Sillybutts/SillyMaxx1400/STLs/Barrels/5x Elite.stl

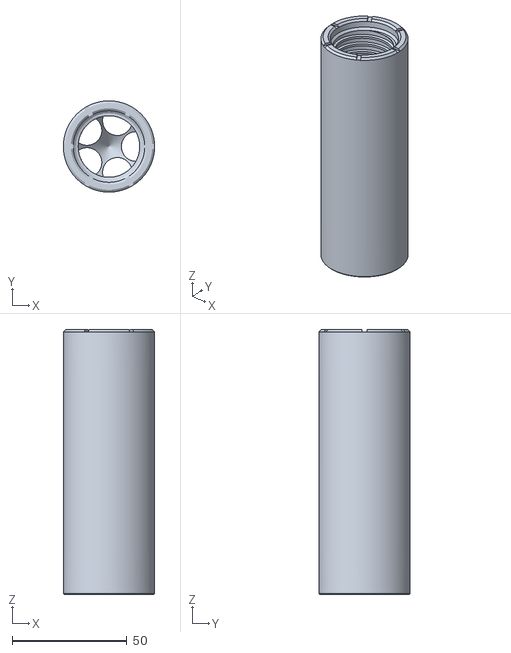
[picture p50: CAD file, 2022-04-14]
STLs/Barrels/5x Elite.stl
39.8 x 39.8 x 115.5
