Sillybutts/SillyMaxx1400/STLs/Gray/Trigger Guard.stl

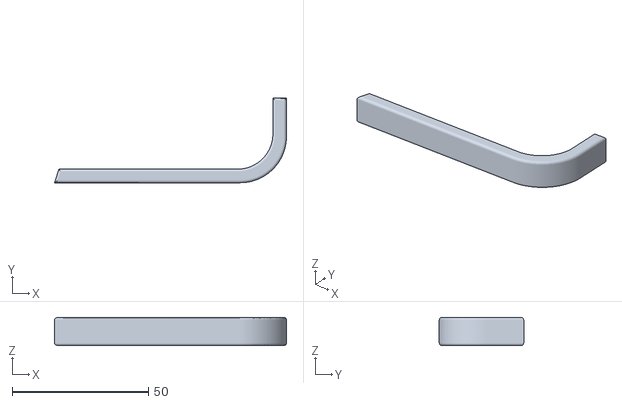
[picture p51: CAD file, 2022-04-14]
STLs/Gray/Trigger Guard.stl
85.2 x 31.0 x 10.4
