Sillybutts/SillyMaxx1400/STLs/Orange/Attachments for top of Faux Tank/TopSight.stl

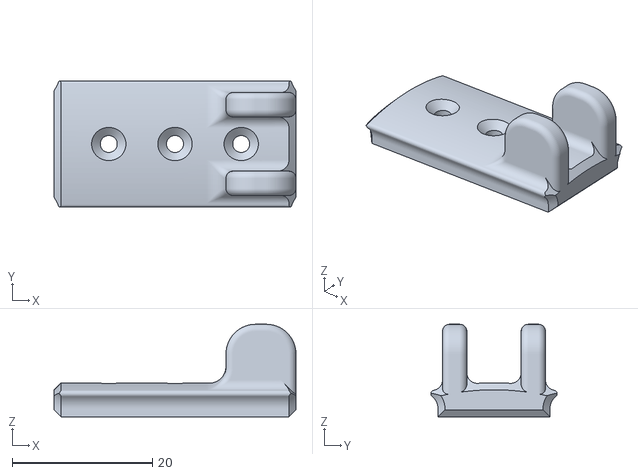
[picture p52: CAD file, 2022-04-14]
STLs/Orange/Attachments for top of Faux Tank/TopSight.stl
34.5 x 18.0 x 13.2
