Sillybutts/SillyMaxx1400/STLs/Orange/TriggerB.stl

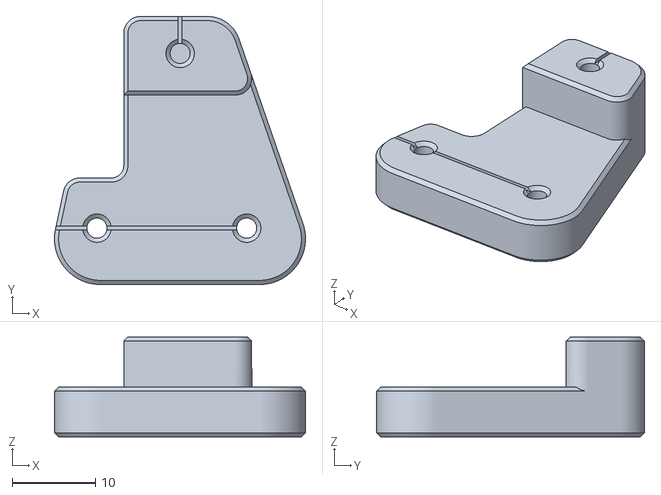
[picture p53: CAD file, 2022-04-14]
STLs/Orange/TriggerB.stl
30.2 x 32.2 x 12.0
