Sillybutts/SillyMaxx1400/STLs/Red/BackTube4PRINTTWO.stl

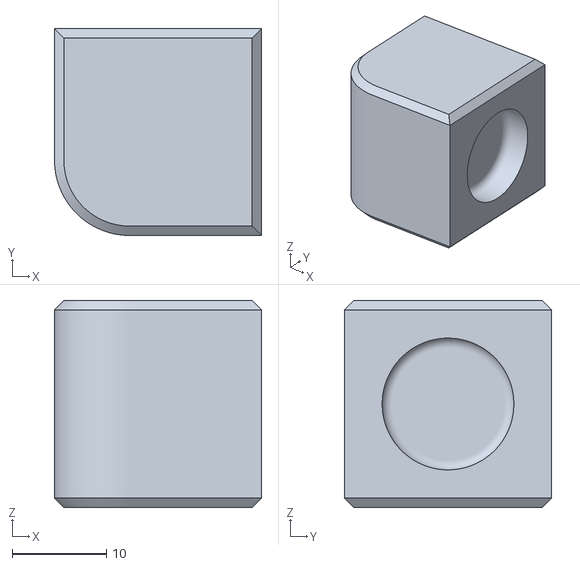
[picture p54: CAD file, 2022-04-14]
STLs/Red/BackTube4PRINTTWO.stl
22.0 x 22.0 x 22.0
