Sillybutts/SillyMaxx1400/STLs/Yellow/PumpGrip.stl

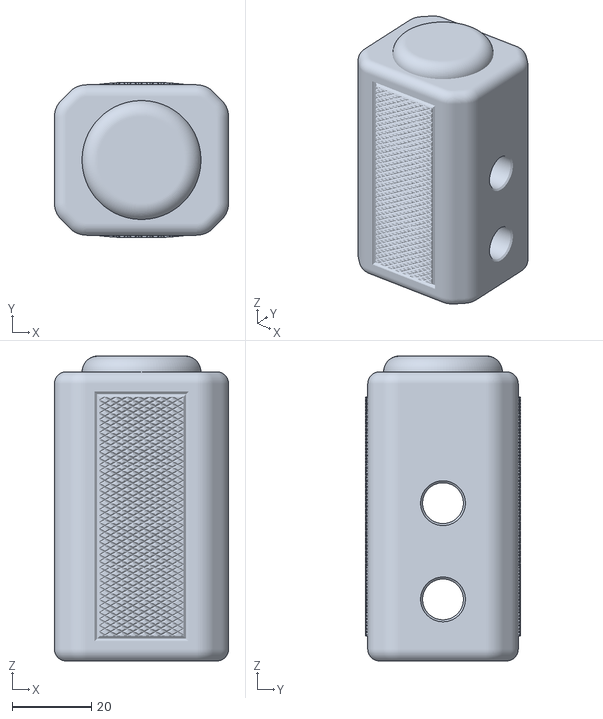
[picture p55: CAD file, 2022-04-14]
STLs/Yellow/PumpGrip.stl
44.0 x 39.1 x 77.0
