Sillybutts/SillyMaxx1400/STLs/Barrels/Mega.stl

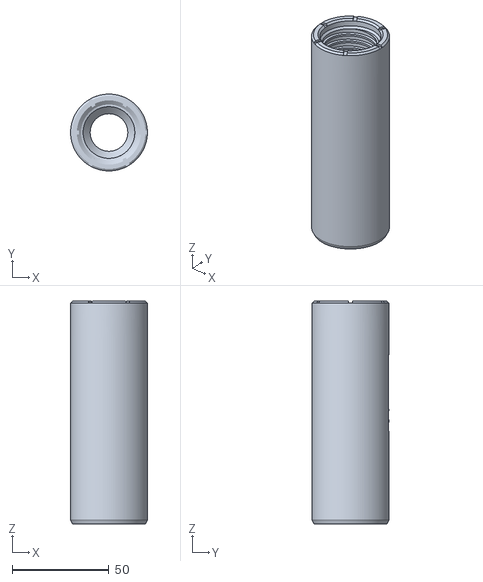
[picture p56: CAD file, 2022-04-14]
STLs/Barrels/Mega.stl
39.8 x 39.8 x 115.5
