Sillybutts/SillyMaxx1400/STLs/Gray/Back Cover.stl

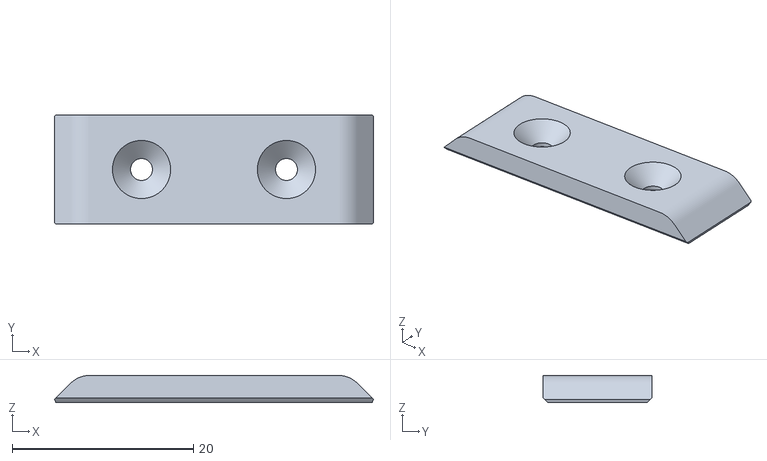
[picture p57: CAD file, 2022-04-14]
STLs/Gray/Back Cover.stl
35.2 x 12.0 x 3.00
