Sillybutts/SillyMaxx1400/STLs/Orange/Attachments for top of Faux Tank/MXL Ammo Holder.stl

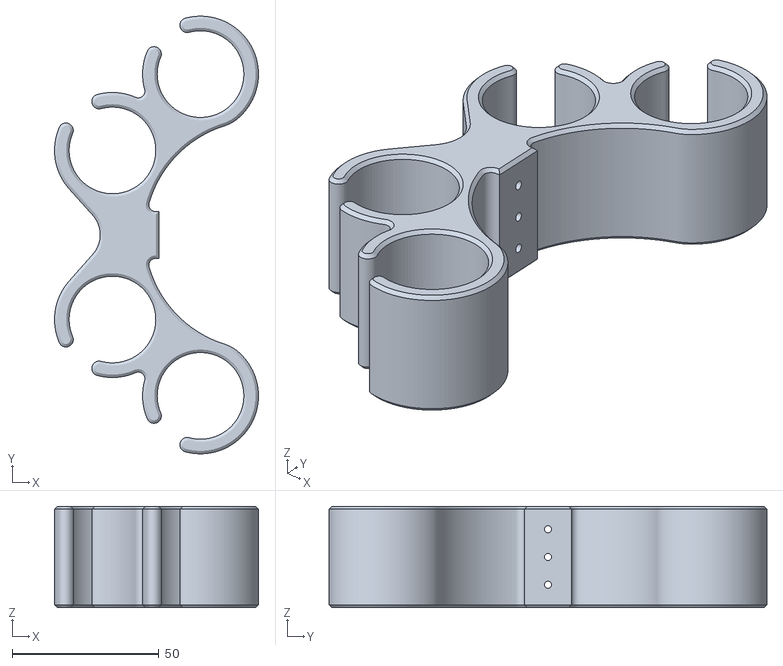
[picture p58: CAD file, 2022-04-14]
STLs/Orange/Attachments for top of Faux Tank/MXL Ammo Holder.stl
69.5 x 149.1 x 34.5
