Sillybutts/SillyMaxx1400/STLs/Orange/TriggerC.stl

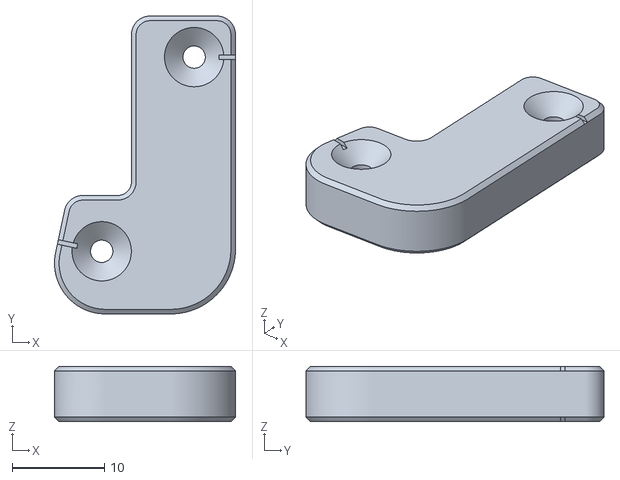
[picture p59: CAD file, 2022-04-14]
STLs/Orange/TriggerC.stl
19.6 x 32.2 x 6.00
