Sillybutts/SillyMaxx1400/STLs/Red/Faux Tank wAttachmentSlot A.stl

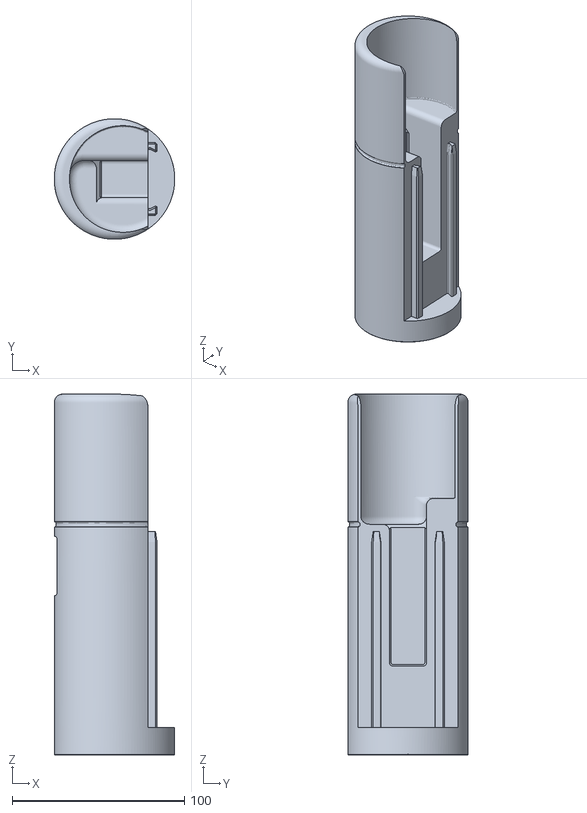
[picture p60: CAD file, 2022-04-14]
STLs/Red/Faux Tank wAttachmentSlot A.stl
70.0 x 70.0 x 209.8
