Sillybutts/SillyMaxx1400/STLs/Barrels/halfinchPVC SMOOTH.stl

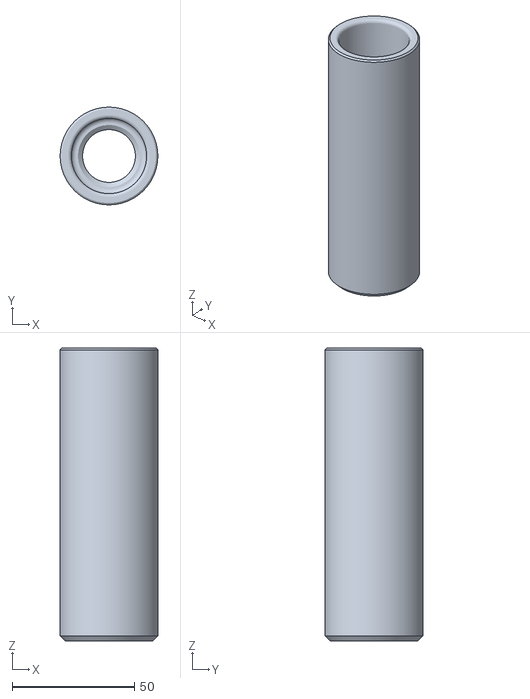
[picture p61: CAD file, 2022-04-14]
STLs/Barrels/halfinchPVC SMOOTH.stl
40.0 x 40.0 x 120.0
