Sillybutts/SillyMaxx1400/STLs/Gray/SmallCover.stl

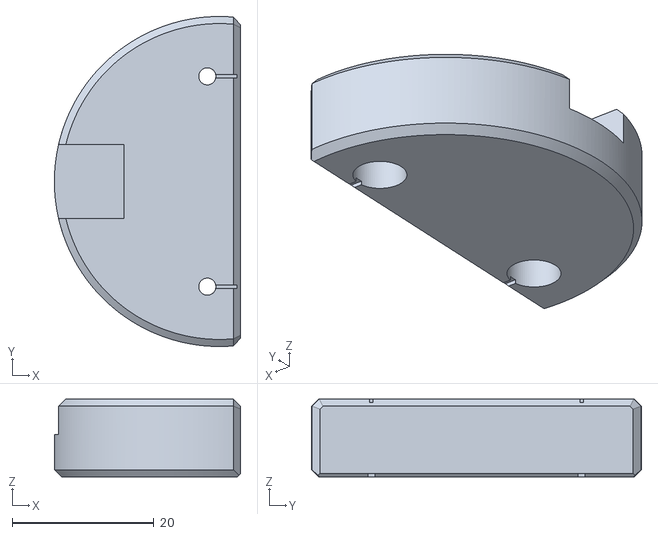
[picture p62: CAD file, 2022-04-14]
STLs/Gray/SmallCover.stl
26.3 x 46.6 x 11.0
