Sillybutts/SillyMaxx1400/STLs/Orange/Top Front Cap.stl

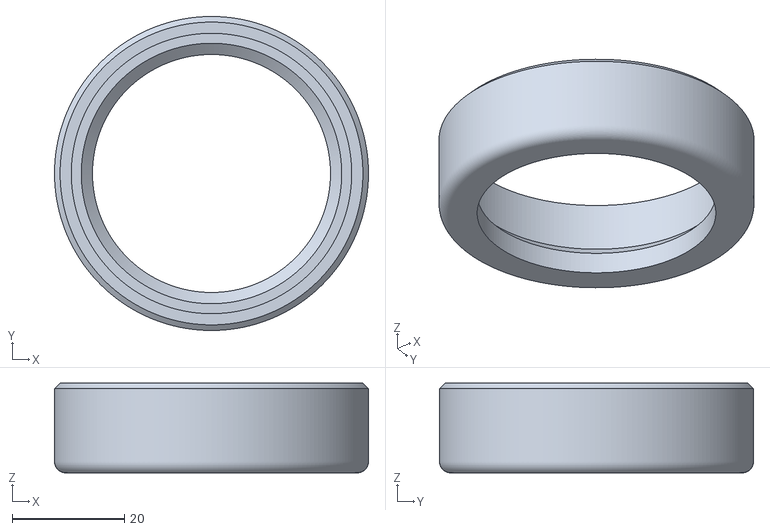
[picture p63: CAD file, 2022-04-14]
STLs/Orange/Top Front Cap.stl
56.0 x 56.0 x 16.0
