Sillybutts/SillyMaxx1400/STLs/Red/BackTube1.stl

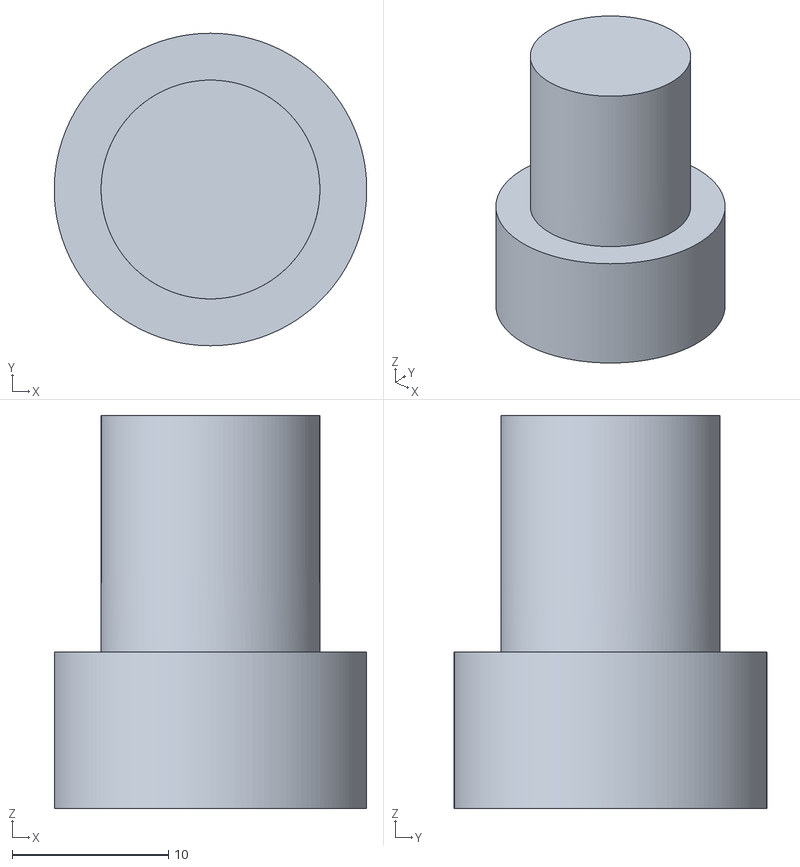
[picture p64: CAD file, 2022-04-14]
STLs/Red/BackTube1.stl
20.0 x 20.0 x 25.1
