Sillybutts/SillyMaxx1400/STLs/Barrels/3x Elite.stl

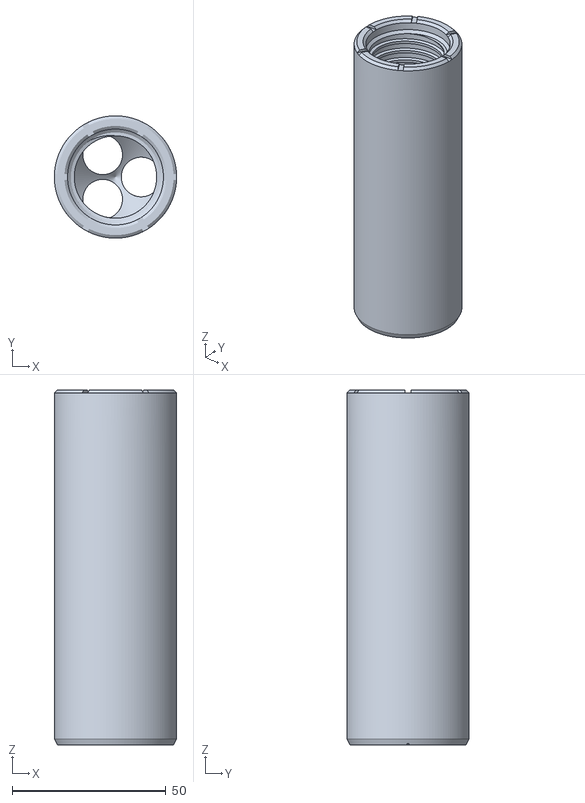
[picture p65: CAD file, 2022-04-14]
STLs/Barrels/3x Elite.stl
39.8 x 39.8 x 115.5
