Sillybutts/SillyMaxx1400/STLs/Gray/GripFrameB.stl

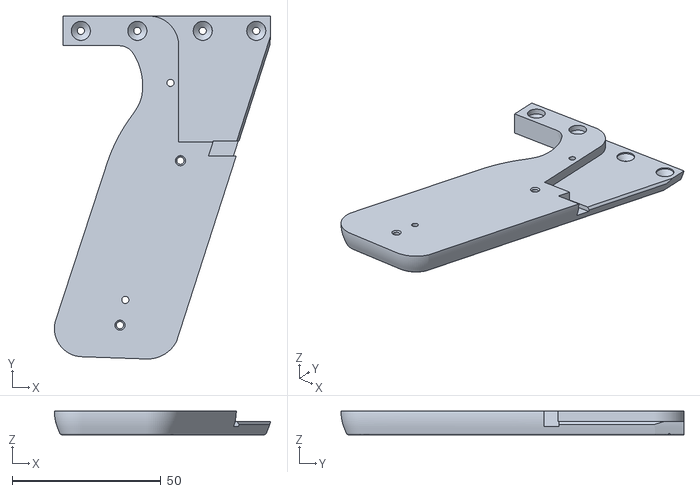
[picture p66: CAD file, 2022-04-14]
STLs/Gray/GripFrameB.stl
72.7 x 115.4 x 8.00
