Sillybutts/SillyMaxx1400/STLs/Red/Faux Tank B.stl

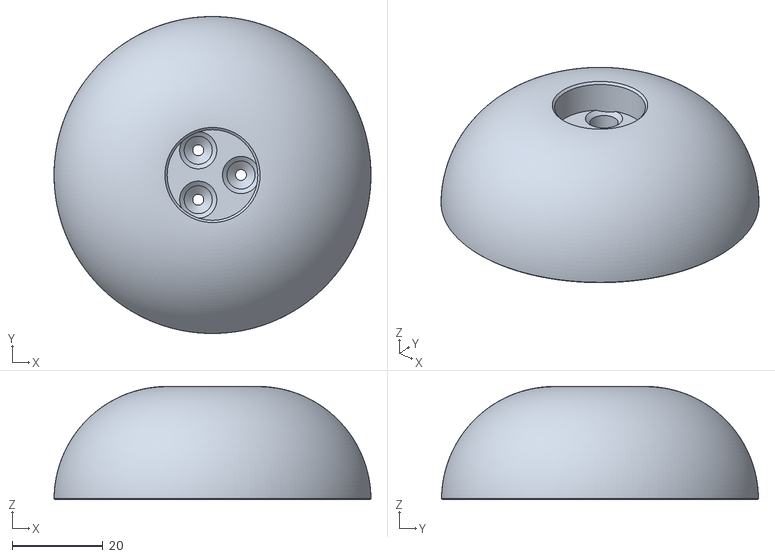
[picture p67: CAD file, 2022-04-14]
STLs/Red/Faux Tank B.stl
70.0 x 70.0 x 25.0
