Sillybutts/SillyMaxx1400/STLs/Barrels/MXL Trivictus.stl

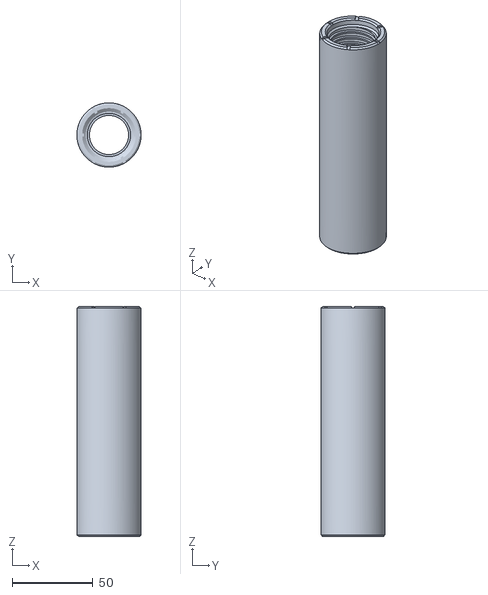
[picture p68: CAD file, 2022-04-14]
STLs/Barrels/MXL Trivictus.stl
39.8 x 39.8 x 142.5
