Sillybutts/SillyMaxx1400/STLs/Gray/Sling Point.stl

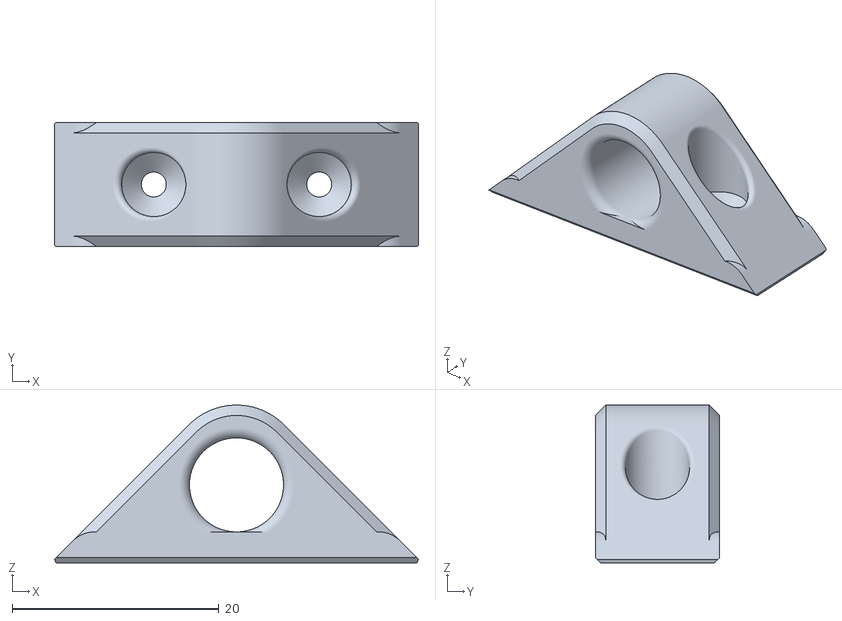
[picture p69: CAD file, 2022-04-14]
STLs/Gray/Sling Point.stl
35.2 x 12.0 x 15.3
