Sillybutts/SillyMaxx1400/STLs/Red/BackTube2PRINTTWO.stl

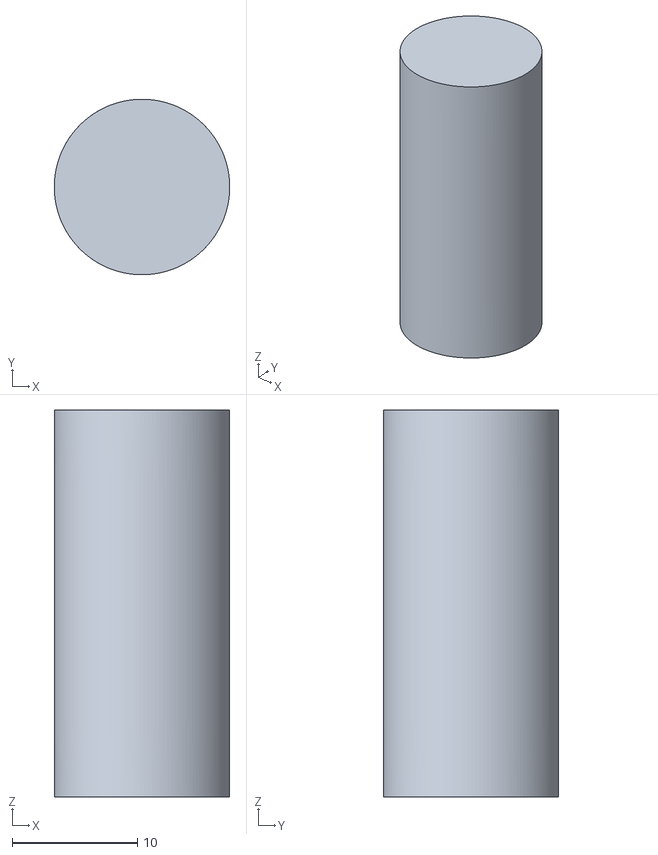
[picture p70: CAD file, 2022-04-14]
STLs/Red/BackTube2PRINTTWO.stl
14.0 x 14.0 x 30.9
