Sillybutts/SillyMaxx1400/STLs/Gray/FrontBlock wSight.stl

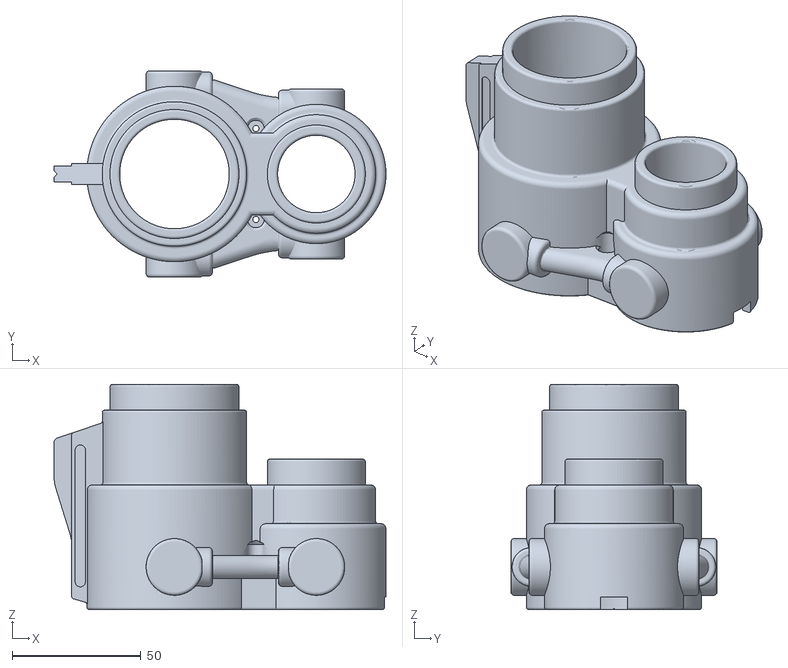
[picture p71: CAD file, 2022-04-14]
STLs/Gray/FrontBlock wSight.stl
128.7 x 80.0 x 87.4
