Sillybutts/SillyMaxx1400/STLs/Gray/BodyBlockA.stl

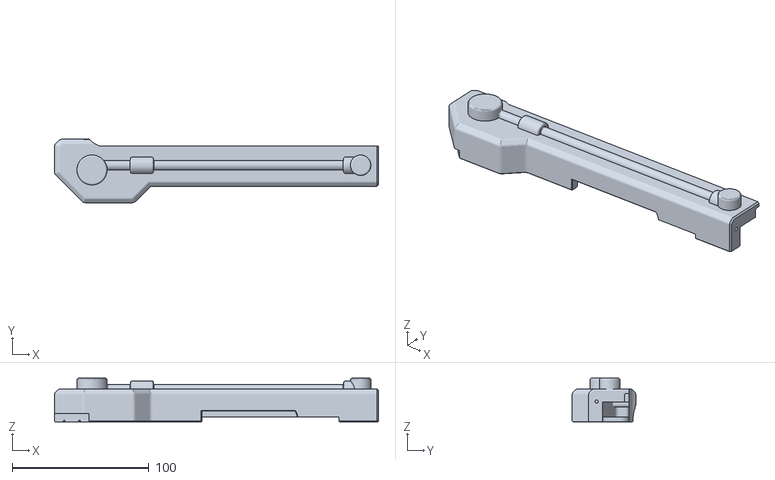
[picture p72: CAD file, 2022-04-14]
STLs/Gray/BodyBlockA.stl
237.0 x 46.5 x 32.0
