Sillybutts/SillyMaxx1400/STLs/Gray/BodyBlockC.stl

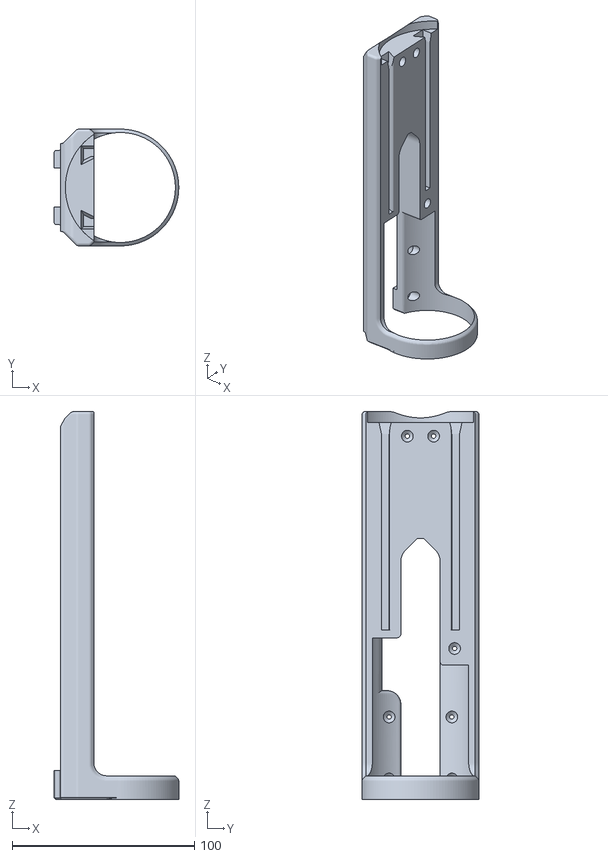
[picture p73: CAD file, 2022-04-14]
STLs/Gray/BodyBlockC.stl
68.3 x 64.1 x 212.8
