Sillybutts/SillyMaxx1400/STLs/Gray/FrontBlock NoSight.stl

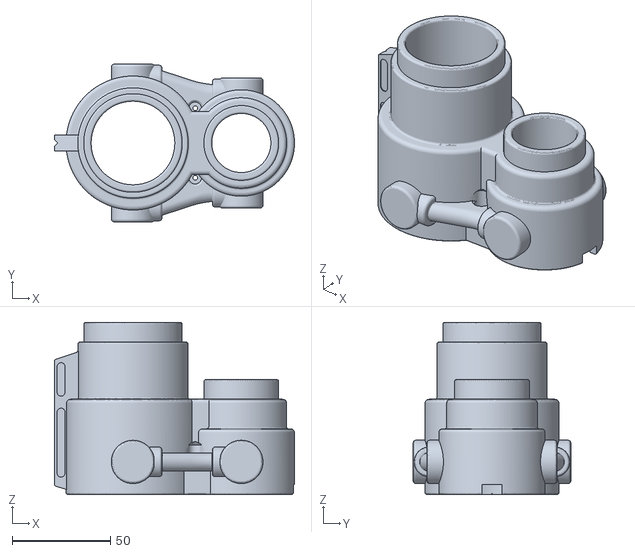
[picture p74: CAD file, 2022-04-14]
STLs/Gray/FrontBlock NoSight.stl
121.8 x 80.0 x 87.4
